ucgosupl/mm_legend_v2/src/code/wall_sensor/wall_sensor_offsets.h

/*
 * file:	wall_sensor_offsets.h
 * author:	GAndaLF
 * brief:	Wall sensor offsets from robot reference point.
 */

#ifndef _WALL_SENSOR_OFFSETS_H_
#define _WALL_SENSOR_OFFSETS_H_

/** Front sensor offset in X axis. */
#define WALL_SENSOR_FRONT_OFFSET_X      32.0f
/** Front sensor offset in Y axis. */
#define WALL_SENSOR_FRONT_OFFSET_Y      34.0f
/** Front sensor angle offset. */
#define WALL_SENSOR_FRONT_OFFSET_A      0.0f

/** Diagonal sensor offset in X axis. */
#define WALL_SENSOR_DIAG_OFFSET_X      35.5f
/** Diagonal sensor offset in Y axis. */
#define WALL_SENSOR_DIAG_OFFSET_Y      26.5f
/** Diagonal sensor angle offset. */
#define WALL_SENSOR_DIAG_OFFSET_A      45.0f

/** Side sensor offset in X axis. */
#define WALL_SENSOR_SIDE_OFFSET_X      43.0f
/** Side sensor offset in Y axis. */
#define WALL_SENSOR_SIDE_OFFSET_Y      20.0f
/** Side sensor angle offset. */
#define WALL_SENSOR_SIDE_OFFSET_A      00.0f

#endif /* _WALL_SENSOR_OFFSETS_H_ */
