ucgosupl/mm_legend_v2/src/code/wall_sensor/adc2dist.c

/*
 * file:	adc2dist.c
 * author:	GAndaLF
 * brief:	Conversion from ADC value to distance in millimeters.
 */

#include "platform_specific.h"

#include "wall_sensor/adc2dist.h"
#include "wall_sensor/wall_sensor.h"

/** Lookup table size equals ADC range. */
#define LOOKUP_TABLE_SIZE       4096

/**
 * Left front sensor lookup table for conversion from ADC value to distance in mm.
 *
 * Table is generated automatically using script scripts/generate_lookups.m
 */
static const uint8_t adc2dist_front_l_lookup[4096] = {
    WALL_NOT_FOUND, WALL_NOT_FOUND, WALL_NOT_FOUND, WALL_NOT_FOUND, WALL_NOT_FOUND, WALL_NOT_FOUND, WALL_NOT_FOUND, WALL_NOT_FOUND,
    WALL_NOT_FOUND, WALL_NOT_FOUND, WALL_NOT_FOUND, WALL_NOT_FOUND, WALL_NOT_FOUND, WALL_NOT_FOUND, WALL_NOT_FOUND, WALL_NOT_FOUND,
    WALL_NOT_FOUND, WALL_NOT_FOUND, WALL_NOT_FOUND, WALL_NOT_FOUND, WALL_NOT_FOUND, WALL_NOT_FOUND, WALL_NOT_FOUND, WALL_NOT_FOUND,
    WALL_NOT_FOUND, WALL_NOT_FOUND, WALL_NOT_FOUND, WALL_NOT_FOUND, WALL_NOT_FOUND, WALL_NOT_FOUND, WALL_NOT_FOUND, WALL_NOT_FOUND,
    WALL_NOT_FOUND, WALL_NOT_FOUND, WALL_NOT_FOUND, WALL_NOT_FOUND, WALL_NOT_FOUND, WALL_NOT_FOUND, WALL_NOT_FOUND, WALL_NOT_FOUND,
    WALL_NOT_FOUND, WALL_NOT_FOUND, WALL_NOT_FOUND, WALL_NOT_FOUND, WALL_NOT_FOUND, WALL_NOT_FOUND, WALL_NOT_FOUND, WALL_NOT_FOUND,
    WALL_NOT_FOUND, WALL_NOT_FOUND, WALL_NOT_FOUND, WALL_NOT_FOUND, WALL_NOT_FOUND, WALL_NOT_FOUND, WALL_NOT_FOUND, WALL_NOT_FOUND,
    WALL_NOT_FOUND, WALL_NOT_FOUND, WALL_NOT_FOUND, WALL_NOT_FOUND, WALL_NOT_FOUND, WALL_NOT_FOUND, WALL_NOT_FOUND, WALL_NOT_FOUND,
    WALL_NOT_FOUND, WALL_NOT_FOUND, WALL_NOT_FOUND, WALL_NOT_FOUND, WALL_NOT_FOUND, WALL_NOT_FOUND, WALL_NOT_FOUND, WALL_NOT_FOUND,
    WALL_NOT_FOUND, WALL_NOT_FOUND, WALL_NOT_FOUND, WALL_NOT_FOUND, WALL_NOT_FOUND, WALL_NOT_FOUND, WALL_NOT_FOUND, WALL_NOT_FOUND,
    WALL_NOT_FOUND, WALL_NOT_FOUND, WALL_NOT_FOUND, WALL_NOT_FOUND, WALL_NOT_FOUND, WALL_NOT_FOUND, WALL_NOT_FOUND, WALL_NOT_FOUND,
    WALL_NOT_FOUND, WALL_NOT_FOUND, WALL_NOT_FOUND, WALL_NOT_FOUND, WALL_NOT_FOUND, WALL_NOT_FOUND, WALL_NOT_FOUND, WALL_NOT_FOUND,
    WALL_NOT_FOUND, WALL_NOT_FOUND, WALL_NOT_FOUND, WALL_NOT_FOUND, WALL_NOT_FOUND, WALL_NOT_FOUND, WALL_NOT_FOUND, WALL_NOT_FOUND,
    WALL_NOT_FOUND, WALL_NOT_FOUND, WALL_NOT_FOUND, WALL_NOT_FOUND, WALL_NOT_FOUND, WALL_NOT_FOUND, WALL_NOT_FOUND, WALL_NOT_FOUND,
    WALL_NOT_FOUND, WALL_NOT_FOUND, WALL_NOT_FOUND, WALL_NOT_FOUND, WALL_NOT_FOUND, WALL_NOT_FOUND, WALL_NOT_FOUND, WALL_NOT_FOUND,
    WALL_NOT_FOUND, WALL_NOT_FOUND, WALL_NOT_FOUND, WALL_NOT_FOUND, WALL_NOT_FOUND, WALL_NOT_FOUND, WALL_NOT_FOUND, WALL_NOT_FOUND,
    WALL_NOT_FOUND, WALL_NOT_FOUND, WALL_NOT_FOUND, WALL_NOT_FOUND, WALL_NOT_FOUND, WALL_NOT_FOUND, WALL_NOT_FOUND, WALL_NOT_FOUND,
    WALL_NOT_FOUND, WALL_NOT_FOUND, WALL_NOT_FOUND, WALL_NOT_FOUND, WALL_NOT_FOUND, WALL_NOT_FOUND, WALL_NOT_FOUND, WALL_NOT_FOUND,
    WALL_NOT_FOUND, WALL_NOT_FOUND, WALL_NOT_FOUND, WALL_NOT_FOUND, WALL_NOT_FOUND, WALL_NOT_FOUND, WALL_NOT_FOUND, WALL_NOT_FOUND,
    WALL_NOT_FOUND, WALL_NOT_FOUND, WALL_NOT_FOUND, WALL_NOT_FOUND, WALL_NOT_FOUND, WALL_NOT_FOUND, WALL_NOT_FOUND, WALL_NOT_FOUND,
    WALL_NOT_FOUND, WALL_NOT_FOUND, WALL_NOT_FOUND, WALL_NOT_FOUND, WALL_NOT_FOUND, WALL_NOT_FOUND, WALL_NOT_FOUND, WALL_NOT_FOUND,
    WALL_NOT_FOUND, WALL_NOT_FOUND, WALL_NOT_FOUND, WALL_NOT_FOUND, WALL_NOT_FOUND, WALL_NOT_FOUND, WALL_NOT_FOUND, WALL_NOT_FOUND,
    WALL_NOT_FOUND, WALL_NOT_FOUND, WALL_NOT_FOUND, WALL_NOT_FOUND, WALL_NOT_FOUND, WALL_NOT_FOUND, WALL_NOT_FOUND, WALL_NOT_FOUND,
    WALL_NOT_FOUND, WALL_NOT_FOUND, WALL_NOT_FOUND, WALL_NOT_FOUND, WALL_NOT_FOUND, WALL_NOT_FOUND, WALL_NOT_FOUND, WALL_NOT_FOUND,
    WALL_NOT_FOUND, WALL_NOT_FOUND, WALL_NOT_FOUND, WALL_NOT_FOUND, WALL_NOT_FOUND, WALL_NOT_FOUND, WALL_NOT_FOUND, WALL_NOT_FOUND,
    WALL_NOT_FOUND, WALL_NOT_FOUND, WALL_NOT_FOUND, WALL_NOT_FOUND, WALL_NOT_FOUND, WALL_NOT_FOUND, WALL_NOT_FOUND, WALL_NOT_FOUND,
    WALL_NOT_FOUND, WALL_NOT_FOUND, WALL_NOT_FOUND, WALL_NOT_FOUND, WALL_NOT_FOUND, WALL_NOT_FOUND, WALL_NOT_FOUND, WALL_NOT_FOUND,
    WALL_NOT_FOUND, WALL_NOT_FOUND, WALL_NOT_FOUND, WALL_NOT_FOUND, WALL_NOT_FOUND, WALL_NOT_FOUND, WALL_NOT_FOUND, WALL_NOT_FOUND,
    WALL_NOT_FOUND, WALL_NOT_FOUND, WALL_NOT_FOUND, WALL_NOT_FOUND, WALL_NOT_FOUND, WALL_NOT_FOUND, WALL_NOT_FOUND, WALL_NOT_FOUND,
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
    {
        return WALL_SENSOR_ERROR;
    }

    return adc2dist_diag_r_lookup[adc];
}

int32_t adc2dist_side_l(int32_t adc)
{
    if ((0 > adc) || (LOOKUP_TABLE_SIZE <= adc))
    {
        return WALL_SENSOR_ERROR;
    }

    return adc2dist_side_l_lookup[adc];
}

int32_t adc2dist_side_r(int32_t adc)
{
    if ((0 > adc) || (LOOKUP_TABLE_SIZE <= adc))
    {
        return WALL_SENSOR_ERROR;
    }

    return adc2dist_side_r_lookup[adc];
}
