ucgosupl/mm_legend_v2/src/code/map/map_internal.h

/*
 * file:	map_internal.h
 * author:	GAndaLF
 * brief:	Functions for use internally in map module - not for public API.
 */

#ifndef _MAP_INTERNAL_H_
#define _MAP_INTERNAL_H_

/** Number of detections before wall is added to the map. */
#define MAP_DETECTION_THRESHOLD         3

/**
 * Initialize wall validation module.
 */
void map_validate_init(void);

/**
 * Report left wall presence/absence detection.
 *
 * @param cell_id           Cell index.
 * @param wall_state        Detected state of the wall.
 */
void map_validate_wall_left(int32_t cell_id, map_wall_state_t wall_state);

/**
 * Report right wall presence/absence detection.
 *
 * @param cell_id           Cell index.
 * @param wall_state        Detected state of the wall.
 */
void map_validate_wall_right(int32_t cell_id, map_wall_state_t wall_state);

/**
 * Report top wall presence/absence detection.
 *
 * @param cell_id           Cell index.
 * @param wall_state        Detected state of the wall.
 */
void map_validate_wall_top(int32_t cell_id, map_wall_state_t wall_state);

/**
 * Report bottom wall presence/absence detection.
 *
 * @param cell_id           Cell index.
 * @param wall_state        Detected state of the wall.
 */
void map_validate_wall_bottom(int32_t cell_id, map_wall_state_t wall_state);

/**
 * Set left wall for a cell with a given id to absent.
 *
 * @param cell_id           Cell id to be updated.
 */
void map_add_left_no_wall(int32_t cell_id);

/**
 * Set right wall for a cell with a given id to absent.
 *
 * @param cell_id           Cell id to be updated.
 */
void map_add_right_no_wall(int32_t cell_id);

/**
 * Set top wall for a cell with a given id to absent.
 *
 * @param cell_id           Cell id to be updated.
 */
void map_add_top_no_wall(int32_t cell_id);

/**
 * Set top wall for a cell with a given id to absent.
 *
 * @param cell_id           Cell id to be updated.
 */
void map_add_bottom_no_wall(int32_t cell_id);

/**
 * Set left wall for a cell with a given id to present.
 *
 * @param cell_id           Cell id to be updated.
 */
void map_add_left_wall(int32_t cell_id);

/**
 * Set right wall for a cell with a given id to present.
 *
 * @param cell_id           Cell id to be updated.
 */
void map_add_right_wall(int32_t cell_id);

/**
 * Set top wall for a cell with a given id to present.
 *
 * @param cell_id           Cell id to be updated.
 */
void map_add_top_wall(int32_t cell_id);

/**
 * Set bottom wall for a cell with a given id to present.
 *
 * @param cell_id           Cell id to be updated.
 */
void map_add_bottom_wall(int32_t cell_id);

/**
 * Calculate adjacent cell index for left wall.
 *
 * Walls seen from current cell are also visible from adjacent cell. This function
 * calculates adjacent cell index for left wall. Walls on maze borders are
 * not seen from any other cells. In this case -1 is returned.
 *
 * @param cell_id           Current cell id.
 *
 * @return                  Adjacent cell id, -1 if current cell on the maze border.
 */
int32_t map_cell_adjacent_to_wall_left_get(int32_t cell_id);

/**
 * Calculate adjacent cell index for right wall.
 *
 * Walls seen from current cell are also visible from adjacent cell. This function
 * calculates adjacent cell index for right wall. Walls on maze borders are
 * not seen from any other cells. In this case -1 is returned.
 *
 * @param cell_id           Current cell id.
 *
 * @return                  Adjacent cell id, -1 if current cell on the maze border.
 */
int32_t map_cell_adjacent_to_wall_right_get(int32_t cell_id);

/**
 * Calculate adjacent cell index for top wall.
 *
 * Walls seen from current cell are also visible from adjacent cell. This function
 * calculates adjacent cell index for top wall. Walls on maze borders are
 * not seen from any other cells. In this case -1 is returned.
 *
 * @param cell_id           Current cell id.
 *
 * @return                  Adjacent cell id, -1 if current cell on the maze border.
 */
int32_t map_cell_adjacent_to_wall_top_get(int32_t cell_id);

/**
 * Calculate adjacent cell index for bottom wall.
 *
 * Walls seen from current cell are also visible from adjacent cell. This function
 * calculates adjacent cell index for bottom wall. Walls on maze borders are
 * not seen from any other cells. In this case -1 is returned.
 *
 * @param cell_id           Current cell id.
 *
 * @return                  Adjacent cell id, -1 if current cell on the maze border.
 */
int32_t map_cell_adjacent_to_wall_bottom_get(int32_t cell_id);

#endif /* _MAP_INTERNAL_H_ */
