ucgosupl/mm_legend_v2/test/hw_test/hbridge/main.c

/*
 * File: main.c
 * Author: GAndaLF
 * Brief: Main file for hw_test_template target.
 */

#include "platform_specific.h"

/* Project includes */
#include "core_init/core_init.h"
#include "vbat/vbat.h"

#include "hbridge_test_task.h"

int main(void)
{
    core_init();

    /* Place your initialisation code here. */
    vbat_task_init();
    hbridge_test_task_init();

    /* Place your application code here. */
    vTaskStartScheduler();

    while (1)
        ;
}
