ucgosupl/mm_legend_v2/test/hw_test/imu/main.c

/*
 * File: main.c
 * Author: GAndaLF
 * Brief: Main file for hw_test_template target.
 */

#include "stm32f4xx.h"
#include "platform_specific.h"

#include "core_init/core_init.h"
#include "logger/logger.h"
#include "vbat/vbat.h"

#include "imu_test_task.h"

int main(void)
{
    core_init();

    /* Place your initialisation code here. */
    vbat_task_init();
    logger_task_init();
    imu_test_task_init();

    /* Place your application code here. */
    vTaskStartScheduler();

    while (1)
        ;
}
