ucgosupl/mm_legend_v2/test/hw_test/motor_linear/motor_linear_task.c

/*
 * file:    motor_linear_task.c
 * author:  GAndaLF
 * brief:   Task for checking linear velocity control loop.
 */

#include "motor_linear_task.h"

#include "platform_specific.h"

#include <stdio.h>

/* Project includes */
#include "button/button.h"
#include "motor/motor.h"

#define SPEED_MM_S          500
#define SPEED_ANGULAR       45
#define SAMPLE_CNT          200

#define MOTOR_IDENT_TASK_STACKSIZE          (configMINIMAL_STACK_SIZE * 8)
#define MOTOR_IDENT_TASK_PRIORITY           (tskIDLE_PRIORITY + 2)

struct motor_params
{
    int32_t left;
    int32_t right;
};

static struct motor_params wheel_data[SAMPLE_CNT];

static void motor_linear_task(void *params);

void motor_linear_task_init(void)
{
    button_init();
    motor_task_init();

    rtos_task_create(motor_linear_task, "motor_l",
                     MOTOR_IDENT_TASK_STACKSIZE, MOTOR_IDENT_TASK_PRIORITY);
}

static void motor_linear_task(void *params)
{
    (void) params;

    int32_t i;
    tick_t last;

    while (1)
    {
        if (0 != button_1_get())
        {
            rtos_delay(2000);

            motor_pid_linear_reset();
            motor_pid_angular_reset();

            motor_vlinear_set(SPEED_MM_S);
            motor_vangular_set(SPEED_ANGULAR);

            /* Collect encoder data every 10ms */
            for (i = 0; i < SAMPLE_CNT; i++)
            {
                last = rtos_tick_count_get();

                wheel_data[i].left = (int32_t)motor_vleft_get();
                wheel_data[i].right = (int32_t)motor_vright_get();

                rtos_delay_until(&last, 10);
            }

            motor_vlinear_set(0);
            motor_vangular_set(0);

            for (i = 0; i < SAMPLE_CNT; i++)
            {
                printf("%d\t%d\n", wheel_data[i].left, wheel_data[i].right);
            }
        }

        if (0 != button_2_get())
        {
            rtos_delay(10);
        }

        rtos_delay(10);
    }
}
