ucgosupl/mm_legend_v2/test/unit_test/vbat/mocks/motor_mocks.hpp

/*
 * file:	motor_mocks.hpp
 * author:	GAndaLF
 * brief:	Mock functions for motor control task.
 */

#ifndef _MOTOR_MOCKS_HPP_
#define _MOTOR_MOCKS_HPP_

using MotorAllOffMock = NoRetNoArgMock;

void motorAllOffMockSet(MotorAllOffMock *mock);

#endif /* _MOTOR_MOCKS_HPP_ */
