ucgosupl/mm_legend_v2/test/hw_test/initial_states/initial_states_task.h

/*
 * file:	initial_states_task.h
 * author:	GAndaLF
 * brief:	Task for initial states measurements.
 */

#ifndef _INITIAL_STATES_TASK_H_
#define _INITIAL_STATES_TASK_H_

/**
 * Initialize initial states measurements task.
 */
void initial_states_test_task_init(void);

#endif /* _POSITION_TASK_H_ */
