ucgosupl/mm_legend_v2/test/hw_test/motor_linear/motor_linear_task.h

/*
 * file:	motor_linear_task.h
 * author:	GAndaLF
 * brief:	Task for checking linear velocity control loop.
 */

#ifndef _MOTOR_IDENT_TASK_H_
#define _MOTOR_IDENT_TASK_H_

/**
 * Initialise motor identification task.
 */
void motor_linear_task_init(void);

#endif /* _MOTOR_IDENT_TASK_H_ */
