ucgosupl/mm_legend_v2/test/hw_test/motor_ident/motor_ident_task.h

/*
 * file:	motor_ident_task.h
 * author:	GAndaLF
 * brief:	Task for motor characteristics identification.
 */

#ifndef _MOTOR_IDENT_TASK_H_
#define _MOTOR_IDENT_TASK_H_

/**
 * Initialise motor identification task.
 */
void motor_ident_task_init(void);

#endif /* _MOTOR_IDENT_TASK_H_ */
