ucgosupl/mm_legend_v2/test/hw_test/wall/wall_test_task.h

/*
 * file:	hbridge_test_task.h
 * author:	GAndaLF
 * brief:	Task for testing wall sensors.
 */

#ifndef _WALL_TEST_TASK_H_
#define _WALL_TEST_TASK_H_

/**
 * Initialise wall sensor test task.
 */
void wall_test_task_init(void);

#endif /* _WALL_TEST_TASK_H_ */
