ucgosupl/mm_legend_v2/test/hw_test/libfixmatrix/libfixmatrix_test_task.h

/*
 * file:	libfixmatrix_test_task.h
 * author:	GAndaLF
 * brief:	Task for testing libfixmatrix library.
 */

#ifndef _LIBFIXMATRIX_TEST_TASK_H_
#define _LIBFIXMATRIX_TEST_TASK_H_

/**
 * Initialise libfixmatrix test task.
 */
void libfixmatrix_test_task_init(void);

#endif /* _LIBFIXMATRIX_TEST_TASK_H_ */
