ucgosupl/mm_legend_v2/test/hw_test/position/position_task.h

/*
 * file:	position_task.h
 * author:	GAndaLF
 * brief:	Task for position estimation hardware test.
 */

#ifndef _POSITION_TASK_H_
#define _POSITION_TASK_H_

/**
 * Initialize position estimation test task.
 */
void position_test_task_init(void);

#endif /* _POSITION_TASK_H_ */
