ucgosupl/mm_legend_v2/test/hw_test/imu/imu_test_task.h

/*
 * file:	imu_test_task.h
 * author:	GAndaLF
 * brief:	Task for testing IMU sensor.
 */

#ifndef _IMU_TEST_TASK_H_
#define _IMU_TEST_TASK_H_

/**
 * Initialise IMU sensor test task.
 */
void imu_test_task_init(void);

#endif /* _IMU_TEST_TASK_H_ */
