ucgosupl/mm_legend_v2/test/hw_test/logger/logger_test_task.h

/*
 * file:	logger_test_task.h
 * author:	GAndaLF
 * brief:	Task for testing data logger.
 */

#ifndef _LOGGER_TEST_TASK_H_
#define _LOGGER_TEST_TASK_H_

/**
 * Initialise data logger test task.
 */
void logger_test_task_init(void);

#endif /* _LOGGER_TEST_TASK_H_ */
