ucgosupl/mm_legend_v2/test/hw_test/hbridge/hbridge_test_task.h

/*
 * file:	hbridge_test_task.h
 * author:	GAndaLF
 * brief:	Task for testing H-bridge functionality.
 */

#ifndef _HBRIDGE_TEST_TASK_H_
#define _HBRIDGE_TEST_TASK_H_

/**
 * Initialise H-bridge test task.
 */
void hbridge_test_task_init(void);

#endif /* _HBRIDGE_TEST_TASK_H_ */
